smaroukis/cygolite-pcb/firmware/platformio-attiny202-pwm/src_experimental/pwm_fade_w_gamma.cpp

#include <Arduino.h>

const uint8_t PWM_PIN = PIN_PA3;  // change to your working PWM pin

const uint8_t gammaTable[256] = {
  0, 0, 0, 0, 0, 0, 0, 0, 0, 0, 0, 0, 0, 0, 0, 0,
  0, 0, 0, 0, 0, 0, 0, 0, 0, 0, 0, 0, 1, 1, 1, 1,
  1, 1, 1, 1, 1, 1, 1, 1, 1, 1, 1, 1, 1, 1, 1, 2,
  2, 2, 2, 2, 2, 2, 2, 2, 3, 3, 3, 3, 3, 3, 3, 4,
  4, 4, 4, 4, 5, 5, 5, 5, 6, 6, 6, 6, 7, 7, 7, 8,
  8, 8, 9, 9, 9, 10, 10, 11, 11, 12, 12, 13, 13, 14, 14, 15,
  15, 16, 16, 17, 18, 18, 19, 20, 20, 21, 22, 23, 23, 24, 25, 26,
  27, 28, 29, 30, 30, 31, 32, 34, 35, 36, 37, 38, 39, 40, 42, 43,
  44, 45, 47, 48, 50, 51, 52, 54, 55, 57, 59, 60, 62, 63, 65, 67,
  69, 70, 72, 74, 76, 78, 80, 82, 84, 86, 88, 90, 93, 95, 97, 99,
  102, 104, 107, 109, 111, 114, 117, 119, 122, 124, 127, 130, 133, 135, 138, 141,
  144, 147, 150, 153, 156, 159, 163, 166, 169, 172, 176, 179, 182, 186, 190, 193,
  197, 200, 204, 208, 211, 215, 219, 223, 227, 231, 235, 239, 243, 247, 251, 255,
  255, 255, 255, 255, 255, 255, 255, 255, 255, 255, 255, 255, 255, 255, 255, 255,
  255, 255, 255, 255, 255, 255, 255, 255, 255, 255, 255, 255, 255, 255, 255, 255,
  255, 255, 255, 255, 255, 255, 255, 255, 255, 255, 255, 255, 255, 255, 255, 255
};

int level = 0;
int stepSize = 1;

void setup() {
  pinMode(PWM_PIN, OUTPUT);
}

void loop() {
  analogWrite(PWM_PIN, gammaTable[level]);

  level += stepSize;

  if (level >= 255) {
    level = 255;
    stepSize = -1;
  }

  if (level <= 0) {
    level = 0;
    stepSize = 1;
  }

  delay(8);
}
